Immanueldavidckp/schematics/docs/housing/internal/housing-closed.png

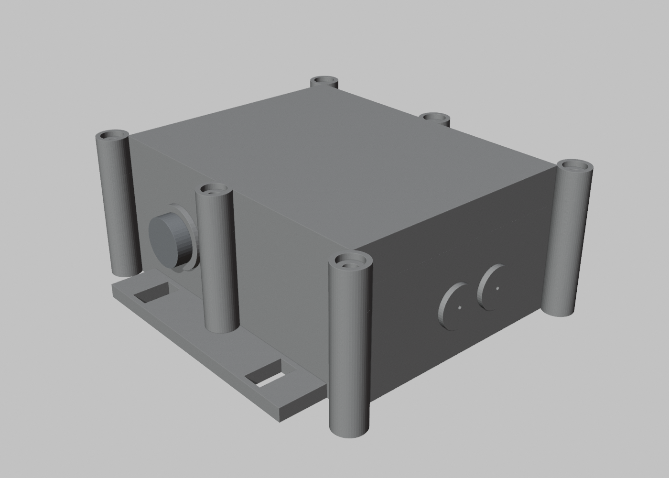
docs/housing/internal/housing-closed.png
