Immanueldavidckp/schematics/docs/housing/internal/housing-exploded.png

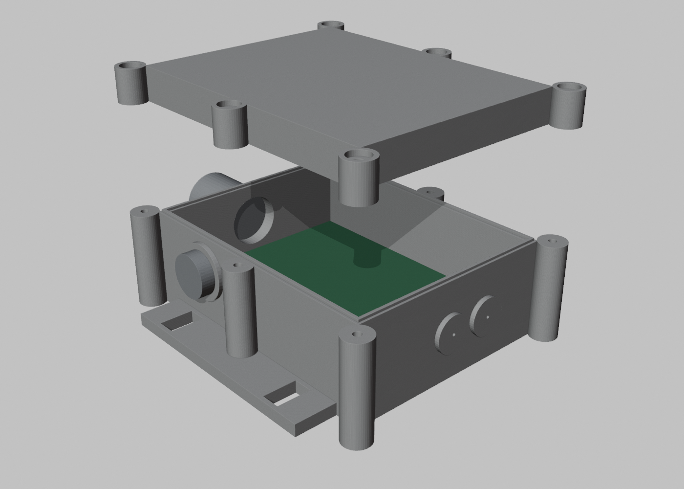
docs/housing/internal/housing-exploded.png
