Immanueldavidckp/schematics/docs/housing/internal/housing-sma-wall.png

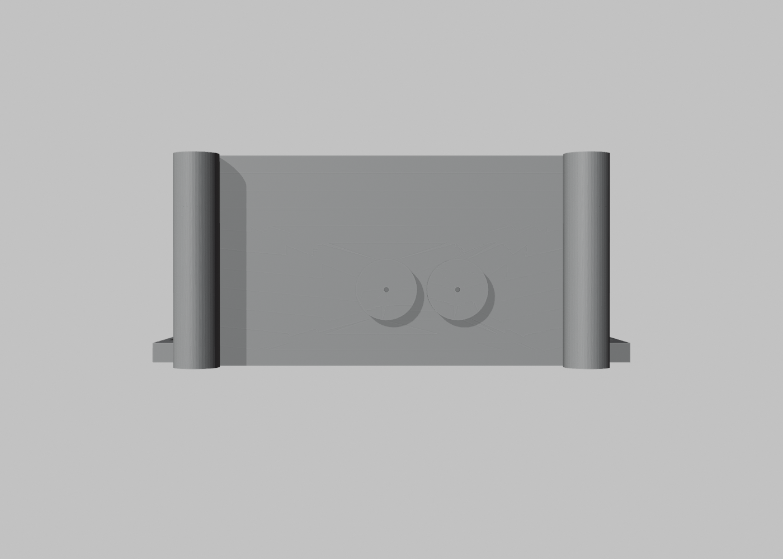
docs/housing/internal/housing-sma-wall.png
