Immanueldavidckp/schematics/tools/pcbroute_lv.py

#!/usr/bin/env python3
"""Route the remaining low-speed nets with the in-repo maze router (path b).

Approved after FreeRouting v2.4.1 was measured malfunctioning on this board
(design-log 2026-09-06). Quality gates, as instructed:

  1. Netclass rules enforced per net, DRC after each net, never loosened.
     A net whose routing raises the DRC error count is ROLLED BACK from the
     last good save and reported as failed - copper that cannot meet the
     rules does not stay on the board.
  2. Progress commit every 25 nets with completion %.
  3. Metrics: vias per net (flag > 4), total vias, routed length vs Manhattan
     distance per net (flag > 2.5x).
  4. No new copper on RF/HV/MV nets (those are locked and finished), none in
     the RF corridor, and none through the U1 lattice or U5 EP via fields.
  5. On plateau: stop with a per-net unrouted list and the blocking cause.

Architecture: pour-first. The board's power architecture IS the L2 GND plane
and the L3 islands (5V0 / SYS / 3V3 / VIN_B / VBAT_MODEM), so power-net pads
are connected by a stub + via into their plane wherever the pad sits over its
pour - one via, near-zero added length. Only what cannot reach a pour is
maze-routed on F/B.

Run:  PYTHONPATH=tools python3 tools/pcbroute_lv.py
"""
import ast
import heapq
import math
import os
import time
import re
import shutil
import subprocess
import sys
from collections import Counter, defaultdict

import pcbnew

sys.path.insert(0, os.path.dirname(os.path.abspath(__file__)))
from pcbgen import PROJ, PCB, mm, pt, canonicalise           # noqa: E402
from netclasses import HV, MV, RF, PWR, BULK                 # noqa: E402

to_mm = pcbnew.ToMM

RES = 0.10
CLR_EDGE = 0.50                 # copper-to-edge board rule for LV
LAST_GOOD = PCB + ".lastgood"
PROTECTED = set(HV) | set(MV) | set(RF)

# (track_width, clearance, via_dia, via_drill) per class
GEO = {
    # Default clearance is 0.20: that is what the board's stock Default
    # netclass carries, and the first run used 0.15 here - DRC (correctly)
    # rejected 12 nets against the class rule. Gate 1 works; the constant
    # was wrong.
    "Default":    (0.20, 0.20, 0.50, 0.30),
    "PWR":        (0.50, 0.20, 0.80, 0.40),
    "MODEM_BULK": (2.00, 0.20, 0.80, 0.40),
    "GND":        (0.50, 0.15, 0.50, 0.30),
}
CLS_CLR = {"HV": 0.60, "MV": 0.60, "RF": 0.30, "GND": 0.15,
           "PWR": 0.20, "MODEM_BULK": 0.20, "Default": 0.20}


def net_class(n):
    if n in HV:
        return "HV"
    if n in MV:
        return "MV"
    if n in RF:
        return "RF"
    if n in PWR:
        return "PWR"
    if n in BULK:
        return "MODEM_BULK"
    if n == "GND":
        return "GND"
    return "Default"


def drc_errors(path):
    """Non-ratsnest DRC error count (the per-net gate)."""
    rpt = path + ".drc"
    subprocess.run(["kicad-cli", "pcb", "drc", "--severity-error",
                    "-o", rpt, path], capture_output=True)
    text = open(rpt).read()
    kinds = re.findall(r"^\[([a-z_]+)\]", text, re.M)
    os.unlink(rpt)
    return sum(1 for k in kinds if k != "unconnected_items")


def git_progress(msg):
    subprocess.run(["git", "-C", PROJ, "add", os.path.basename(PCB)],
                   capture_output=True)
    subprocess.run(["git", "-C", PROJ, "commit", "-q", "-m",
                    msg + "\n\nCo-Authored-By: Claude Opus 5 (1M context) "
                    "<noreply@anthropic.com>"], capture_output=True)


def main(single_net=None, rip=None):
    # --rip: negotiation for the endgame. A net that fails with walled pad
    # entries lost its lanes to nets routed EARLIER (measured: C5.1/NRST had
    # 0/196 free start cells, sealed by VBAT_SENSE, CANH_T and GND vias that
    # are each individually legal). The named nets' UNLOCKED copper near the
    # starved net's pads is removed TEXTUALLY (board.Remove() poisons the
    # SWIG wrappers on Python 3.14 - measured core dumps; the adopt tool's
    # file-level rip is the proven pattern), the ripped copy is loaded, the
    # starved net routes FIRST, the ripped signal nets after. All-or-nothing:
    # any failure exits without saving, so the real board file never holds a
    # ripped-but-unrouted state. No rule changes - only the ORDER in which
    # the same rules are satisfied.
    if rip:
        from pcbgen import _split_forms
        rip = [n for n in rip if n not in PROTECTED]
        pre = pcbnew.LoadBoard(PCB)
        anchors_r = [(p.GetPosition().x / 1e6, p.GetPosition().y / 1e6)
                     for f in pre.GetFootprints()
                     for p in f.Pads() if p.GetNetname() == single_net]
        del pre
        RIP_R = float(os.environ.get("LV_RIP_R", "4"))
        txt = open(PCB, encoding="utf-8").read()
        body = txt[txt.index("\n") + 1: txt.rstrip().rfind(")")]
        kept, n_rip = [], 0
        for fo in _split_forms(body):
            tag = re.match(r"\(\s*([A-Za-z_0-9]+)", fo).group(1)
            drop = False
            if tag in ("segment", "via") and "(locked yes)" not in fo:
                mnet = re.search(r'\(net "([^"]*)"\)', fo)
                mxy = re.search(r"\((?:start|at) ([-\d.]+) ([-\d.]+)\)", fo)
                if mnet and mxy and mnet.group(1) in rip:
                    fx, fy = float(mxy.group(1)), float(mxy.group(2))
                    drop = any(abs(fx - ax) < RIP_R and abs(fy - ay) < RIP_R
                               for ax, ay in anchors_r)
            if drop:
                n_rip += 1
            else:
                kept.append(fo)
        head = txt[:txt.index("\n") + 1]
        tail = txt[txt.rstrip().rfind(")"):]
        # keep the .kicad_pcb extension: LoadBoard picks its format plugin
        # from the extension and returns None for anything else
        riptmp = PCB[:-len(".kicad_pcb")] + "-riptmp.kicad_pcb"
        open(riptmp, "w", encoding="utf-8").write(head + "".join(kept) + tail)
        print(f"ripped {n_rip} unlocked items of {sorted(rip)} "
              f"within {RIP_R:.0f} mm of {single_net}")
        board = pcbnew.LoadBoard(riptmp)
        os.unlink(riptmp)
    else:
        board = pcbnew.LoadBoard(PCB)
    LAYERS = [pcbnew.F_Cu, pcbnew.B_Cu]

    bb = board.GetBoardEdgesBoundingBox()
    x0, y0 = to_mm(bb.GetLeft()), to_mm(bb.GetTop())
    x1, y1 = to_mm(bb.GetRight()), to_mm(bb.GetBottom())
    NX, NY = int((x1 - x0) / RES) + 1, int((y1 - y0) / RES) + 1
    print(f"grid {NX} x {NY} at {RES} mm")

    def cell(x, y):
        return (int(round((x - x0) / RES)), int(round((y - y0) / RES)))

    def pos(ix, iy):
        return (x0 + ix * RES, y0 + iy * RES)

    # ---- no-go regions (both layers, for ALL new copper) -----------------
    nogo = []
    # RF corridor: everything outboard of x = 76.8 is CPWG + fence + U.FL
    nogo.append((76.8, y0, x1, y1, "RF corridor"))
    for ref, pads in (("U1", [str(i) for i in range(85, 113)]), ("U5", ["9"])):
        fp = next(f for f in board.GetFootprints() if f.GetReference() == ref)
        xs, ys, xe, ye = 1e9, 1e9, -1e9, -1e9
        for p in fp.Pads():
            if p.GetNumber() in pads:
                b2 = p.GetBoundingBox()
                xs = min(xs, to_mm(b2.GetLeft())); ys = min(ys, to_mm(b2.GetTop()))
                xe = max(xe, to_mm(b2.GetRight())); ye = max(ye, to_mm(b2.GetBottom()))
        nogo.append((xs - 0.3, ys - 0.3, xe + 0.3, ye + 0.3, ref + " via field"))
    for r in nogo:
        print(f"  no-go: {r[4]}  x {r[0]:.1f}..{r[2]:.1f} y {r[1]:.1f}..{r[3]:.1f}")

    # ---- obstacles --------------------------------------------------------
    # (net, layers, x, y, hw, hh)
    obst = []
    for f in board.GetFootprints():
        for p in f.Pads():
            b2 = p.GetBoundingBox()
            obst.append((p.GetNetname(), [l for l in p.GetLayerSet().CuStack()],
                         to_mm(b2.GetCenter().x), to_mm(b2.GetCenter().y),
                         to_mm(b2.GetWidth()) / 2, to_mm(b2.GetHeight()) / 2,
                         f.GetReference()))
    for t in board.GetTracks():
        if isinstance(t, pcbnew.PCB_VIA):
            obst.append((t.GetNetname(), LAYERS,
                         to_mm(t.GetPosition().x), to_mm(t.GetPosition().y),
                         to_mm(t.GetWidth()) / 2, to_mm(t.GetWidth()) / 2, ""))
        else:
            a, b2 = t.GetStart(), t.GetEnd()
            w = to_mm(t.GetWidth()) / 2
            ax, ay, bx, by = to_mm(a.x), to_mm(a.y), to_mm(b2.x), to_mm(b2.y)
            n = max(1, int(math.hypot(bx - ax, by - ay) / RES))
            for i in range(n + 1):
                tt = i / n
                # the true layer is kept even when it is an INNER one:
                # FreeRouting routes on GND_L2/PWR_L3, and a through-via
                # must clear that copper (measured: MODEM_BULK vias landed
                # 0.05..0.15 mm from SIM_RST on GND_L2 - invisible to a
                # 2-layer grid model)
                obst.append((t.GetNetname(), [t.GetLayer()],
                             ax + (bx - ax) * tt, ay + (by - ay) * tt, w, w, ""))
    print(f"obstacles: {len(obst)}")
    placed = []

    def build(netname, my_clr, half, via_mode=False):
        """via_mode: the grid gates VIA sites - a through via lands on every
        copper layer, so inner-layer obstacles block BOTH surface grids."""
        grids = [bytearray(NX * NY) for _ in LAYERS]
        trace = None
        if os.environ.get("LV_TRACE"):
            tx, ty = map(float, os.environ["LV_TRACE"].split(","))
            trace = cell(tx, ty)

        def block(g, ox, oy, rx, ry):
            # nogo/edge regions only: plain rectangles
            i0 = int(math.floor((ox - rx - x0) / RES))
            j0 = int(math.floor((oy - ry - y0) / RES))
            i1 = int(math.ceil((ox + rx - x0) / RES))
            j1 = int(math.ceil((oy + ry - y0) / RES))
            for j in range(max(0, j0), min(NY - 1, j1) + 1):
                row = j * NX
                for i in range(max(0, i0), min(NX - 1, i1) + 1):
                    g[row + i] = 1

        def block_pad(g, ox, oy, hw, hh, reach):
            # EXACT distance to the copper rectangle, like DRC measures it.
            # A box halo overestimates the corners by (sqrt(2)-1)*reach - up
            # to ~0.2 mm - and that inflation is precisely what erased the
            # legal diagonal passages around the U5/U6/U7 pin fields
            # (27/113 routed, everything else walled in).
            r2 = reach * reach
            i0 = int(math.floor((ox - hw - reach - x0) / RES))
            j0 = int(math.floor((oy - hh - reach - y0) / RES))
            i1 = int(math.ceil((ox + hw + reach - x0) / RES))
            j1 = int(math.ceil((oy + hh + reach - y0) / RES))
            for j in range(max(0, j0), min(NY - 1, j1) + 1):
                row = j * NX
                py = y0 + j * RES
                dy = abs(py - oy) - hh
                if dy < 0:
                    dy = 0.0
                dy2 = dy * dy
                for i in range(max(0, i0), min(NX - 1, i1) + 1):
                    px = x0 + i * RES
                    dx = abs(px - ox) - hw
                    if dx < 0:
                        dx = 0.0
                    if dx * dx + dy2 < r2 - 1e-12:
                        g[row + i] = 1

        for onet, lays, ox, oy, hw, hh, _oref in obst + placed:
            if onet == netname:
                continue
            oc = net_class(onet) if onet else "HV"
            clr = max(my_clr, CLS_CLR.get(oc, 0.15))
            # the 1.5 mm HV-to-LV rule: HV copper in the left strip of
            # HV_ZONE (x < 20; the buck arm is the BUCK_HV rescope at 0.60)
            if oc == "HV" and ox < 20.0:
                clr = 1.50
            inner = via_mode and any(l not in (pcbnew.F_Cu, pcbnew.B_Cu)
                                     for l in lays)
            for li, lay in enumerate(LAYERS):
                if not inner and lay not in lays:
                    continue
                if trace is not None and \
                        abs(ox - (x0 + trace[0] * RES)) <= hw + clr + half and \
                        abs(oy - (y0 + trace[1] * RES)) <= hh + clr + half:
                    print(f"      TRACE L{li} blocked by [{onet}] ref={_oref!r} "
                          f"at ({ox:.2f},{oy:.2f}) hw={hw:.2f} hh={hh:.2f} "
                          f"clr={clr:.2f}")
                block_pad(grids[li], ox, oy, hw, hh, clr + half)
        for gx0, gy0, gx1, gy1, _n in nogo:
            for g in grids:
                block(g, (gx0 + gx1) / 2, (gy0 + gy1) / 2,
                      (gx1 - gx0) / 2 + half, (gy1 - gy0) / 2 + half)
        e = int(math.ceil((CLR_EDGE + half) / RES - 1e-9)) + 1
        for g in grids:
            for j in range(NY):
                row = j * NX
                for i in range(NX):
                    if i < e or i >= NX - e or j < e or j >= NY - e:
                        g[row + i] = 1
        return grids

    def open_pad_entries(netname, tg, half):
        """Unblock the legal axial entry lane into each of this net's pads.

        A 0.5 mm-pitch LQFP pad has a legal entry: a track on the pad's long
        axis keeps 0.5 - 0.15 - half >= class clearance to the neighbouring
        pins. But that window is a +-0.05 mm line, and the box halos of the
        neighbours bury it - measured: U2.44 had 0/48 free goal cells while
        the flood reached 268k cells everywhere else. This opens the axis
        lane ON the pad plus up to 12 cells beyond each tip, re-verifying
        every lane cell against all obstacles EXCEPT sibling pads of the
        same footprint (the axial geometry to siblings is legal by
        construction; anything else - another part's pad, a via, a track -
        still blocks)."""
        mypads = [(o, r) for o in obst
                  for r in [o[6]] if o[0] == netname and o[6]]
        for (onet, lays, cx, cy, hw, hh, ref), _r in mypads:
            vert = hh >= hw
            both = abs(hh - hw) < 0.2      # round/square (THT) pads: 2 lanes
            # the ENTRY hop is emitted at w_hop = min(class w, pad_cap), so
            # cells near this pad are judged with the effective half-width,
            # not the class one - that mismatch is the whole reason lanes
            # near siblings are legal at all
            half_eff = min(half, max(0.20, min(2 * hw, 2 * hh)) / 2)
            # Sibling pads are excluded from lane blocking ONLY when they are
            # LATERAL neighbours - offset perpendicular to the lane axis, the
            # single-row case where the axial geometry is legal at class
            # clearance by construction. A sibling AHEAD along the lane must
            # still block: on U3's LGA grid the 3V3 lane extended straight
            # through the IMU's GND and NC pads (measured: shorting_items).
            # HV-in-strip siblings always block (1.5 mm rule, no exception).
            def sib_skip(o, axis):
                """True when sibling o may be ignored for THIS lane axis.

                Per-lane, and ARITHMETIC, not faith: a lateral sibling is
                skippable only when the lane's copper actually clears it -
                at U3's 0.5 mm LGA pitch a PWR-width entry has zero margin
                and 'legal by construction' measured 0.11 mm (regressions).
                0.055 covers the half-cell grid snap; the extra RES/(2*sqrt2)
                covers diagonal sag through force-opened lane cells, where
                the A* corner-cut test cannot see the wall (measured: a 3V3
                elbow at 0.190 mm from U2.23 against the 0.20 rule)."""
                if o[6] != ref:
                    return False
                if o[0] in HV and o[2] < 20.0:
                    return False          # HV-in-strip: 1.5 mm rule, no pass
                oc2 = net_class(o[0]) if o[0] else "HV"
                need = max(CLS_CLR.get(net_class(netname), 0.2),
                           CLS_CLR.get(oc2, 0.15)) + half + 0.055 + \
                    RES / (2.0 * math.sqrt(2.0))
                if axis == "v":
                    return abs(o[3] - cy) <= hh + 0.15 and \
                        (abs(o[2] - cx) - o[4]) >= need
                return abs(o[2] - cx) <= hw + 0.15 and \
                    (abs(o[3] - cy) - o[5]) >= need

            near = [o for o in obst + placed
                    if o[0] != netname
                    and abs(o[2] - cx) < 4.0 and abs(o[3] - cy) < 4.0]

            def lane_cell_ok(px, py, lay, axis):
                for o in near:
                    on2, l2, ox, oy, ohw, ohh, _r = o
                    if lay not in l2:
                        continue
                    oc = net_class(on2) if on2 else "HV"
                    clr = max(CLS_CLR.get(net_class(netname), 0.2),
                              CLS_CLR.get(oc, 0.15))
                    if on2 in HV and ox < 20.0:
                        clr = 1.50
                    ddx = max(abs(px - ox) - ohw, 0.0)
                    ddy = max(abs(py - oy) - ohh, 0.0)
                    d2 = ddx * ddx + ddy * ddy
                    if d2 >= (clr + half) ** 2 - 1e-12:
                        continue          # clear at class width
                    # sibling exemption, EXACT and per cell: the pad-level
                    # arithmetic approved lanes whose actual row sits off the
                    # pad axis (measured 0.190 mm to U2.23 vs the 0.20 rule,
                    # twice). An opened cell must clear the sibling FOR REAL
                    # at the emitted entry width (w_hop), plus diagonal sag -
                    # opened cells bypass the A* corner-cut wall test.
                    if sib_skip(o, axis) and \
                            d2 >= (clr + half_eff +
                                   RES / (2.0 * math.sqrt(2.0))) ** 2:
                        continue
                    return False
                for gx0, gy0, gx1, gy1, _n in nogo:
                    if gx0 - half <= px <= gx1 + half and \
                            gy0 - half <= py <= gy1 + half:
                        return False
                return True

            for li, lay in enumerate(LAYERS):
                if lay not in lays:
                    continue
                if vert or both:
                    ci = int(round((cx - x0) / RES))
                    j0 = int(round((cy - hh - y0) / RES)) - 25
                    j1 = int(round((cy + hh - y0) / RES)) + 25
                    for j in range(max(1, j0), min(NY - 2, j1) + 1):
                        px, py = pos(ci, j)
                        # every lane cell is verified - including on-pad
                        # cells, because a track on J1.4's own pad can still
                        # sit closer than 1.5 mm to the HV pin next to it
                        if lane_cell_ok(px, py, lay, "v"):
                            tg[li][j * NX + ci] = 0
                if (not vert) or both:
                    cj = int(round((cy - y0) / RES))
                    i0 = int(round((cx - hw - x0) / RES)) - 25
                    i1 = int(round((cx + hw - x0) / RES)) + 25
                    for i in range(max(1, i0), min(NX - 2, i1) + 1):
                        px, py = pos(i, cj)
                        if lane_cell_ok(px, py, lay, "h"):
                            tg[li][cj * NX + i] = 0

    def astar(tg, vg, starts, goals):
        goalset = set(goals)
        if not goalset:
            return None
        gx = sum(g[1] for g in goals) / len(goals)
        gy = sum(g[2] for g in goals) / len(goals)
        openh, best, came = [], {}, {}
        for s in starts:
            best[s] = 0.0
            heapq.heappush(openh, (math.hypot(s[1] - gx, s[2] - gy), 0.0, s, None))
        NB = [(1, 0, 1.0), (-1, 0, 1.0), (0, 1, 1.0), (0, -1, 1.0),
              (1, 1, 1.4142), (1, -1, 1.4142), (-1, 1, 1.4142), (-1, -1, 1.4142)]
        while openh:
            _, g, cur, parent = heapq.heappop(openh)
            if cur in came:
                continue
            came[cur] = parent
            if cur in goalset:
                path = [cur]
                while came[path[-1]] is not None:
                    path.append(came[path[-1]])
                return path[::-1]
            li, ix, iy = cur
            for dx, dy, w in NB:
                nx_, ny_ = ix + dx, iy + dy
                if not (0 <= nx_ < NX and 0 <= ny_ < NY) or tg[li][ny_ * NX + nx_]:
                    continue
                # no corner-cutting: a diagonal between two halo-legal cells
                # can pass RES/(2*sqrt(2)) closer to a pad corner than either
                # endpoint (measured: SYS at 0.1963 vs the 0.20 rule against
                # U9.2 - the +1 that killed every pour batch). Requiring both
                # orthogonal neighbours free keeps the swept segment inside
                # tested cells without shrinking any engineered lane.
                if dx and dy and (tg[li][iy * NX + nx_] or
                                  tg[li][ny_ * NX + ix]):
                    continue
                nxt, ng = (li, nx_, ny_), g + w
                if ng < best.get(nxt, 1e18):
                    best[nxt] = ng
                    heapq.heappush(openh, (ng + math.hypot(nx_ - gx, ny_ - gy),
                                           ng, nxt, cur))
            for lj in range(2):
                if lj == li or vg[lj][iy * NX + ix] or vg[li][iy * NX + ix]:
                    continue
                nxt, ng = (lj, ix, iy), g + 14
                if ng < best.get(nxt, 1e18):
                    best[nxt] = ng
                    heapq.heappush(openh, (ng + math.hypot(ix - gx, iy - gy),
                                           ng, nxt, cur))
        return None

    def pad_cells(p):
        b2 = p.GetBoundingBox()
        cx, cy = to_mm(b2.GetCenter().x), to_mm(b2.GetCenter().y)
        hw, hh = to_mm(b2.GetWidth()) / 2, to_mm(b2.GetHeight()) / 2
        lays = [l for l in p.GetLayerSet().CuStack()]
        out = []
        for li, lay in enumerate(LAYERS):
            if lay not in lays:
                continue
            i0, j0 = cell(cx - hw * 0.9, cy - hh * 0.9)
            i1, j1 = cell(cx + hw * 0.9, cy + hh * 0.9)
            for j in range(max(0, j0), min(NY - 1, j1) + 1):
                for i in range(max(0, i0), min(NX - 1, i1) + 1):
                    out.append((li, i, j))
        return out

    # ---- clusters: BFS over the connectivity graph's DIRECT edges --------
    # GetConnectedItems(item) with no type filter returns just the item, and
    # even typed queries return only DIRECTLY touching items (measured:
    # C81.1 -> 1 via, not the cluster). So the cluster is computed here: BFS
    # over per-type direct-edge queries, zone fills included.
    CONN_TYPES = (pcbnew.PCB_PAD_T, pcbnew.PCB_TRACE_T,
                  pcbnew.PCB_VIA_T, pcbnew.PCB_ZONE_T)

    def clusters(netname):
        conn = board.GetConnectivity()
        items = []
        for f in board.GetFootprints():
            for p in f.Pads():
                if p.GetNetname() == netname:
                    items.append(p)
        for t in board.GetTracks():
            if t.GetNetname() == netname:
                items.append(t)
        for z in board.Zones():
            if not z.GetIsRuleArea() and z.GetNetname() == netname:
                items.append(z)
        byid = {i.m_Uuid.AsString(): i for i in items}
        seen, out = set(), []
        for k in byid:
            if k in seen:
                continue
            stack, comp = [k], []
            while stack:
                c = stack.pop()
                if c in seen:
                    continue
                seen.add(c)
                comp.append(c)
                it = byid[c]
                for T in CONN_TYPES:
                    for j in conn.GetConnectedItems(it, T):
                        jk = j.m_Uuid.AsString()
                        if jk in byid and jk not in seen:
                            stack.append(jk)
            group = [byid[c] for c in comp
                     if byid[c].Type() == pcbnew.PCB_PAD_T]
            extra = [byid[c] for c in comp
                     if byid[c].Type() in (pcbnew.PCB_TRACE_T,
                                           pcbnew.PCB_VIA_T)]
            has_zone = any(byid[c].Type() == pcbnew.PCB_ZONE_T for c in comp)
            out.append((group or [byid[comp[0]]], extra, has_zone))
        # the pour-connected cluster first, then by pad count. The tap loop
        # must SKIP zone-connected clusters: without the flag it re-tapped
        # the already-merged cluster every round (all size-1 clusters sort
        # arbitrarily) and the count never dropped.
        out.sort(key=lambda ge: (not ge[2], -len(ge[0])))
        return out

    # ---- emit helpers -----------------------------------------------------
    stats = {"vias": 0}

    def emit_path(path, net, w, vd, vdr):
        nv, tl = 0, 0.0
        runs, prev = [], None
        for cur in path:
            if prev is not None:
                if prev[0] != cur[0]:
                    runs.append(["via", cur, None, None])
                else:
                    d = (cur[1] - prev[1], cur[2] - prev[2])
                    if runs and runs[-1][0] == "seg" and \
                            runs[-1][3] == (prev[0], d) and runs[-1][2] == prev:
                        runs[-1][2] = cur
                    else:
                        runs.append(["seg", prev, cur, (prev[0], d)])
            prev = cur
        for kind, a, b2, meta in runs:
            if kind == "via":
                li, ix, iy = a
                v = pcbnew.PCB_VIA(board)
                v.SetPosition(pt(*pos(ix, iy)))
                v.SetWidth(mm(vd)); v.SetDrill(mm(vdr))
                v.SetNet(net); v.SetLayerPair(pcbnew.F_Cu, pcbnew.B_Cu)
                board.Add(v)
                nv += 1
                placed.append((net.GetNetname(), LAYERS, *pos(ix, iy),
                               vd / 2, vd / 2, ""))
            else:
                li = meta[0]
                t = pcbnew.PCB_TRACK(board)
                t.SetStart(pt(*pos(*a[1:]))); t.SetEnd(pt(*pos(*b2[1:])))
                t.SetWidth(mm(w)); t.SetLayer(LAYERS[li]); t.SetNet(net)
                board.Add(t)
                seg = math.hypot(b2[1] - a[1], b2[2] - a[2]) * RES
                tl += seg
                n_ = max(abs(b2[1] - a[1]), abs(b2[2] - a[2]), 1)
                for k in range(n_ + 1):
                    fx = a[1] + (b2[1] - a[1]) * k / n_
                    fy = a[2] + (b2[2] - a[2]) * k / n_
                    placed.append((net.GetNetname(), [LAYERS[li]],
                                   x0 + fx * RES, y0 + fy * RES, w / 2, w / 2, ""))
        stats["vias"] += nv
        return nv, tl

    # ---- pour taps ---------------------------------------------------------
    # net -> [(zone, inner_layer, window)] - the FILLED polygon is what a tap
    # via must hit. The first run tested the bounding box only: vias landed in
    # fill voids (clearance holes around other copper), never connected, the
    # cluster count never dropped, and each power net sprayed up to 12 dead
    # vias that then walled off every later net.
    pours = defaultdict(list)
    for z in board.Zones():
        if z.GetIsRuleArea():
            continue
        for l in z.GetLayerSet().CuStack():
            if l in (pcbnew.F_Cu, pcbnew.B_Cu):
                continue
            zb = z.GetBoundingBox()
            pours[z.GetNetname()].append(
                (z, l, (to_mm(zb.GetLeft()) + 0.6, to_mm(zb.GetTop()) + 0.6,
                        to_mm(zb.GetRight()) - 0.6, to_mm(zb.GetBottom()) - 0.6)))

    def tap_pour(netname, group, tg, vg, vd, vdr, w, net):
        """Maze a stub from the cluster to a via site that HITS the net's
        filled inner-layer pour. Returns the emitted items (for rollback) or
        None. The via site is verified against the FILLED polygon and the
        stub is a routed path, not a blind line."""
        zl = pours.get(netname)
        if not zl:
            return None
        goals = []
        for z, lay, (wx0, wy0, wx1, wy1) in zl:
            i0, j0 = cell(wx0, wy0)
            i1, j1 = cell(wx1, wy1)
            for j in range(max(0, j0), min(NY - 1, j1) + 1):
                for i in range(max(0, i0), min(NX - 1, i1) + 1):
                    if vg[0][j * NX + i] or vg[1][j * NX + i]:
                        continue
                    x, y = pos(i, j)
                    if z.HitTestFilledArea(lay, pt(x, y), 0):
                        goals.append((0, i, j))
                        goals.append((1, i, j))
        if not goals:
            return None
        starts = []
        for p in group:
            starts += pad_cells(p)
        path = astar(tg, vg, starts, set(goals))
        if path is None:
            return None
        mark = len(placed)
        items_before = set(id(t) for t in board.GetTracks())
        emit_path(path, net, w, vd, vdr)
        # a through via at the endpoint reaches the inner pour; if the path
        # already ended with a layer change, that via is the tap
        li, ix, iy = path[-1]
        need_via = len(path) < 2 or path[-2][0] == path[-1][0]
        if need_via:
            v = pcbnew.PCB_VIA(board)
            v.SetPosition(pt(*pos(ix, iy)))
            v.SetWidth(mm(vd)); v.SetDrill(mm(vdr))
            v.SetNet(net); v.SetLayerPair(pcbnew.F_Cu, pcbnew.B_Cu)
            board.Add(v)
            stats["vias"] += 1
            placed.append((netname, LAYERS, *pos(ix, iy), vd / 2, vd / 2, ""))
        new_items = [t for t in board.GetTracks() if id(t) not in items_before]
        return new_items, mark

    # GND: the L2 solid plane
    for z in board.Zones():
        if z.GetZoneName() == "L2_GND_solid":
            pours["GND"] = [(z, board.GetLayerID("In1.Cu"),
                             (x0 + 2.0, y0 + 2.0, x1 - 2.0, y1 - 2.0))]

    # ---- the work list -----------------------------------------------------
    def refill():
        board.BuildListOfNets()
        pcbnew.ZONE_FILLER(board).Fill(board.Zones())

    def refresh_connectivity():
        board.BuildConnectivity()

    # ---- island taps -------------------------------------------------------
    # KiCad's connectivity treats a ZONE as ONE item, so a pour that fills as
    # several disconnected islands still merges its clusters()' BFS into one
    # cluster - route_net() then reports the net complete while DRC counts an
    # unconnected edge per island split (measured: 104 of the 150-edge v11
    # plateau were exactly these, on GND/3V3/5V0/SYS). A filled island with no
    # net via / PTH pad inside it can only be reached through its own copper:
    # bond it with one via at a spot where another fill of the same net (the
    # L2 plane, an L3 island, or the opposite surface pour) lies underneath.

    def net_anchors(netname):
        anchors = [t.GetPosition() for t in board.GetTracks()
                   if t.GetNetname() == netname
                   and t.GetClass() == "PCB_VIA"]
        for f in board.GetFootprints():
            for p in f.Pads():
                if p.GetNetname() == netname and \
                        p.GetAttribute() == pcbnew.PAD_ATTRIB_PTH:
                    anchors.append(p.GetPosition())
        return anchors

    def net_fills(netname):
        out = []
        for z in board.Zones():
            if z.GetIsRuleArea() or z.GetNetname() != netname:
                continue
            for lay in z.GetLayerSet().CuStack():
                out.append((z, lay))
        return out

    def orphan_islands(netname):
        """(zone, layer, outline-index, bbox) of every fill island holding no
        via / through pad of the net."""
        anchors = net_anchors(netname)
        out = []
        for z, lay in net_fills(netname):
            polys = z.GetFilledPolysList(lay)
            for oi in range(polys.OutlineCount()):
                bb = polys.Outline(oi).BBox()
                if any(bb.Contains(a) and polys.Contains(a, oi)
                       for a in anchors):
                    continue
                out.append((z, lay, oi, bb))
        return out

    def island_taps(netname, net, vd, vdr, my_clr):
        """Place the bonding vias. Returns how many were added; refills and
        rebuilds connectivity when any were."""
        orphans = orphan_islands(netname)
        if not orphans:
            return 0
        vg = build(netname, my_clr, vd / 2, via_mode=True)
        fills = net_fills(netname)
        added = []
        for z, lay, oi, bb in orphans:
            polys = z.GetFilledPolysList(lay)
            i0, j0 = cell(to_mm(bb.GetLeft()), to_mm(bb.GetTop()))
            i1, j1 = cell(to_mm(bb.GetRight()), to_mm(bb.GetBottom()))
            spot = None
            for j in range(max(0, j0), min(NY - 1, j1) + 1):
                for i in range(max(0, i0), min(NX - 1, i1) + 1):
                    if vg[0][j * NX + i] or vg[1][j * NX + i]:
                        continue
                    x, y = pos(i, j)
                    # a fresh via is not in vg: keep new ones apart
                    if any((x - ax) ** 2 + (y - ay) ** 2 < 0.9 ** 2
                           for ax, ay in added):
                        continue
                    p_ = pt(x, y)
                    if not polys.Contains(p_, oi):
                        continue
                    if any(z2.HitTestFilledArea(l2, p_, 0)
                           for z2, l2 in fills
                           if not (z2 is z and l2 == lay)):
                        spot = (x, y)
                        break
                if spot:
                    break
            if spot is None:
                if os.environ.get("LV_DEBUG"):
                    print(f"    DEBUG island (layer {lay}) at "
                          f"({to_mm(bb.GetLeft()):.1f},{to_mm(bb.GetTop()):.1f})"
                          f" has no legal tap spot")
                continue
            v = pcbnew.PCB_VIA(board)
            v.SetPosition(pt(*spot))
            v.SetWidth(mm(vd)); v.SetDrill(mm(vdr))
            v.SetNet(net); v.SetLayerPair(pcbnew.F_Cu, pcbnew.B_Cu)
            board.Add(v)
            stats["vias"] += 1
            placed.append((netname, LAYERS, *spot, vd / 2, vd / 2, ""))
            added.append(spot)
        if added:
            if os.environ.get("LV_DEBUG"):
                print(f"    DEBUG island taps: {len(added)} vias "
                      f"({len(orphans)} orphan islands)")
            refill()
            refresh_connectivity()
        return len(added)

    if single_net == "--finish--":
        refill()
        pcbnew.SaveBoard(PCB, board)
        canonicalise(PCB)
        print("CHILD_FINISHED")
        return

    refill()
    refresh_connectivity()

    if single_net == "--list--":
        all_nets = sorted({p.GetNetname() for f in board.GetFootprints()
                           for p in f.Pads()
                           if p.GetNetname() and p.GetNetname() not in PROTECTED})
        for n in all_nets:
            if len(clusters(n)) > 1 or orphan_islands(n):
                print(f"TODO {n}")
        return

    if single_net == "--spans--":
        all_nets = {p.GetNetname() for f in board.GetFootprints()
                    for p in f.Pads()
                    if p.GetNetname() and p.GetNetname() not in PROTECTED}
        for n in sorted(all_nets):
            xs, ys = [], []
            for f in board.GetFootprints():
                for p in f.Pads():
                    if p.GetNetname() == n:
                        xs.append(to_mm(p.GetPosition().x))
                        ys.append(to_mm(p.GetPosition().y))
            if len(xs) > 1:
                print(f"SPAN {max(xs)-min(xs)+max(ys)-min(ys):.1f} {n}")
        return

    def route_net(netname):
        """Route one net to a single cluster. On failure ALL of this net's
        partial copper is REMOVED (board.Remove on tracks/vias is safe -
        verified; the footprint segfault in SKILL.md does not apply) so a
        failed net cannot wall off the nets after it. Returns
        (ok, cause, vias, length, manhattan)."""
        cls = net_class(netname)
        w, my_clr, vd, vdr = GEO[cls]
        net = board.FindNet(netname)
        nv_net, tl_net, man_net = 0, 0.0, 0.0

        def pad_cap(p):
            b2 = p.GetBoundingBox()
            return max(0.20, min(to_mm(b2.GetWidth()), to_mm(b2.GetHeight())))

        def fail(cause):
            # No in-memory rollback (board.Remove crashes at scale). The
            # child decides: with zero progress it exits unsaved; with
            # partial progress it SAVES and reports CHILD_PARTIAL - the
            # copper is legal, only the remaining edges requeue.
            return False, cause, nv_net, tl_net, man_net

        # The FIRST tap into a virgin pour does not reduce the pad-cluster
        # count (it merges a cluster with the pour, not with another pad
        # cluster) - the drop comes when the second cluster taps in. So the
        # stagnation window is 3 rounds, not 1.
        nv_net += island_taps(netname, net, vd, vdr, my_clr)

        best_cl, stagnant = None, 0
        for _round in range(40):
            refresh_connectivity()
            cl = clusters(netname)
            if len(cl) <= 1:
                if orphan_islands(netname):
                    return fail("orphan pour islands with no legal tap spot")
                return True, "", nv_net, tl_net, man_net
            if os.environ.get("LV_DEBUG"):
                sizes = [len(g) for g, _e, _z in cl][:8]
                print(f"    DEBUG round {_round}: {len(cl)} clusters "
                      f"(pad counts {sizes})")
            if best_cl is None or len(cl) < best_cl:
                best_cl, stagnant = len(cl), 0
            else:
                stagnant += 1
                if stagnant >= 3:
                    return fail(f"cluster count stuck at {len(cl)}")
            tg = build(netname, my_clr, w / 2)
            vg = build(netname, my_clr, vd / 2, via_mode=True)
            open_pad_entries(netname, tg, w / 2)
            tapped = False
            for group, _extra, hz in cl[1:]:
                if hz:
                    continue          # already reaches the pour
                r = tap_pour(netname, group, tg, vg, vd, vdr, w, net)
                if r is not None:
                    if os.environ.get("LV_DEBUG"):
                        gp = group[0]
                        nm = "?"
                        try:
                            nm = (gp.GetParentFootprint().GetReference()
                                  + "." + gp.GetPadNumber())
                        except Exception:
                            nm = gp.GetClass()
                        items2, _mk = r
                        vpos = [f"({to_mm(t.GetPosition().x):.1f},"
                                f"{to_mm(t.GetPosition().y):.1f})"
                                for t in items2
                                if isinstance(t, pcbnew.PCB_VIA)]
                        print(f"    DEBUG tapped {nm} vias at "
                              f"{vpos}")
                    nv_net += 1
                    tapped = True
                    break
            if tapped:
                last_cl = len(cl)
                continue
            pairs = []
            for i in range(len(cl)):
                for j in range(i + 1, len(cl)):
                    for pa in cl[i][0]:
                        for pb in cl[j][0]:
                            d = (pa.GetPosition() - pb.GetPosition()).EuclideanNorm()
                            pairs.append((d, i, j, pa, pb))
            if not pairs:
                return fail("no pad pair")
            pairs.sort(key=lambda t: t[0])
            # try up to 12 candidate pairs: the closest pair's endpoint can
            # be pocketed while another cluster pair routes fine - and on the
            # multi-cluster pour nets, quitting at the 4th candidate left
            # every easy pair BEHIND the first hard one unrouted (measured:
            # 3V3 stalled whole at U3.5->U3.10 with 24 other edges pending)
            path = None
            for _d, i, j, pa, pb in pairs[:12]:
            # A 2.0 mm MODEM_BULK track cannot ENTER a 1210 pad cluster at
            # 0.2 clearance (measured: C81.1 goals 0/286 free). The last
            # approach is physically capped by the endpoint pad's own width -
            # the pad is the cross-section limit; the RAIL requirement is
            # carried by the pour and the wide mid-run.
            # min() of the endpoint caps: the hop must ENTER BOTH pads, and
            # a 1.5 mm track cannot enter an 0603 (measured on C43.1). The
            # rail current rides the pour; the last approach is pad-limited.
                w_hop = min(w, pad_cap(pa), pad_cap(pb))
                if w_hop < w:
                    tg = build(netname, my_clr, w_hop / 2)
                    open_pad_entries(netname, tg, w_hop / 2)
                starts = []
                for p in cl[i][0]:
                    starts += pad_cells(p)
                for it in cl[i][1]:
                    if isinstance(it, pcbnew.PCB_VIA):
                        c = cell(to_mm(it.GetPosition().x),
                                 to_mm(it.GetPosition().y))
                        starts += [(0, *c), (1, *c)]
                goals = []
                for p in cl[j][0]:
                    goals += pad_cells(p)
                path = astar(tg, vg, starts, goals)
                if path is not None:
                    break
                if w_hop < w:
                    # restore the class-width grid for the next candidate
                    tg = build(netname, my_clr, w / 2)
                    open_pad_entries(netname, tg, w / 2)
            if path is None and os.environ.get("LV_DEBUG"):
                free_s = sum(1 for li, i, j in starts if not tg[li][j * NX + i])
                free_g = sum(1 for li, i, j in goals if not tg[li][j * NX + i])
                print(f"    DEBUG starts {free_s}/{len(starts)} free, "
                      f"goals {free_g}/{len(goals)} free")
                # a SEALED terminal (0 free cells) is starved by the few nets
                # whose copper covers its own cells - name THOSE, not the
                # whole flood boundary: the global wall histogram dilutes the
                # actual sealers into noise (measured: U2.8 sealed by nets
                # that never reached the top-3 rip candidates)
                cls2 = net_class(netname)
                clr_half = GEO[cls2][0] / 2
                for label, cells, nfree in (("start", starts, free_s),
                                            ("goal", goals, free_g)):
                    if nfree > 0:
                        continue
                    seal = Counter()
                    for li, i, j in cells:
                        px, py = pos(i, j)
                        for on2, l2, ox, oy, ohw, ohh, _r in obst + placed:
                            if on2 == netname or LAYERS[li] not in l2:
                                continue
                            oc2 = net_class(on2) if on2 else "HV"
                            c2 = max(GEO[cls2][1], CLS_CLR.get(oc2, 0.15))
                            if on2 in HV and ox < 20.0:
                                c2 = 1.50
                            if abs(px - ox) <= ohw + c2 + clr_half and \
                                    abs(py - oy) <= ohh + c2 + clr_half:
                                seal[on2 or "netless"] += 1
                                break
                    print(f"    DEBUG pad seal ({label}): "
                          f"{dict(seal.most_common(5))}")
                from collections import deque
                seen, dq = set(), deque()
                for c in starts:
                    li, i, j = c
                    if not tg[li][j * NX + i]:
                        seen.add(c); dq.append(c)
                while dq:
                    li, i, j = dq.popleft()
                    for dx, dy in ((1,0),(-1,0),(0,1),(0,-1),
                                   (1,1),(1,-1),(-1,1),(-1,-1)):
                        ni, nj = i + dx, j + dy
                        if 0 <= ni < NX and 0 <= nj < NY and \
                                not tg[li][nj * NX + ni] and \
                                (li, ni, nj) not in seen:
                            seen.add((li, ni, nj)); dq.append((li, ni, nj))
                    lj = 1 - li
                    if not vg[lj][j * NX + i] and not vg[li][j * NX + i] \
                            and (lj, i, j) not in seen:
                        seen.add((lj, i, j)); dq.append((lj, i, j))
                xs = [pos(i, j) for li, i, j in list(seen)[:100000]]
                if xs:
                    print(f"    DEBUG flood {len(seen)} cells, x range "
                          f"{min(x for x,_ in xs):.1f}..{max(x for x,_ in xs):.1f}, "
                          f"y {min(y for _,y in xs):.1f}..{max(y for _,y in xs):.1f}")
                else:
                    print(f"    DEBUG flood 0 cells - ALL start cells blocked")
                # name the walls: which nets' halos form the pocket boundary
                cls = net_class(netname)
                my_clr = GEO[cls][1]
                half = GEO[cls][0] / 2
                wall = Counter()
                frontier = 0
                for (li, i, j) in list(seen)[:60000]:
                    for dx, dy in ((1,0),(-1,0),(0,1),(0,-1)):
                        ni, nj = i + dx, j + dy
                        if not (0 <= ni < NX and 0 <= nj < NY) or \
                                not tg[li][nj * NX + ni]:
                            continue
                        frontier += 1
                        if frontier > 4000:
                            break
                        px, py = pos(ni, nj)
                        hit = None
                        for on2, l2, ox, oy, ohw, ohh, oref in obst + placed:
                            if on2 == netname or LAYERS[li] not in l2:
                                continue
                            oc = net_class(on2) if on2 else "HV"
                            clr = max(my_clr, CLS_CLR.get(oc, 0.15))
                            if on2 in HV and ox < 20.0:
                                clr = 1.50
                            if abs(px - ox) <= ohw + clr + half and \
                                    abs(py - oy) <= ohh + clr + half:
                                hit = f"{on2 or 'netless'}"
                                break
                        wall[hit or "edge/nogo"] += 1
                    if frontier > 4000:
                        break
                print(f"    DEBUG pocket walls: "
                      f"{dict(wall.most_common(8))}")
                shown = 0
                for (li, i, j) in list(seen)[:60000]:
                    if shown >= 6:
                        break
                    for dx, dy in ((1,0),(-1,0),(0,1),(0,-1)):
                        ni, nj = i + dx, j + dy
                        if not (0 <= ni < NX and 0 <= nj < NY) or \
                                not tg[li][nj * NX + ni]:
                            continue
                        px, py = pos(ni, nj)
                        hit = None
                        for on2, l2, ox, oy, ohw, ohh, oref in obst + placed:
                            if on2 == netname or LAYERS[li] not in l2:
                                continue
                            oc = net_class(on2) if on2 else "HV"
                            clr = max(my_clr, CLS_CLR.get(oc, 0.15))
                            if on2 in HV and ox < 20.0:
                                clr = 1.50
                            if abs(px - ox) <= ohw + clr + half and \
                                    abs(py - oy) <= ohh + clr + half:
                                hit = on2
                                break
                        if hit is None:
                            print(f"    DEBUG unknown wall cell L{li} "
                                  f"({px:.2f},{py:.2f})")
                            shown += 1
                            break
            if path is None:
                cause = (f"no path "
                         f"{pa.GetParentFootprint().GetReference()}.{pa.GetNumber()}"
                         f" -> "
                         f"{pb.GetParentFootprint().GetReference()}.{pb.GetNumber()}")
                return fail(cause)
            nv, tl = emit_path(path, net, w_hop, vd, vdr)
            nv_net += nv
            tl_net += tl
            man_net += (abs(to_mm(pa.GetPosition().x - pb.GetPosition().x))
                        + abs(to_mm(pa.GetPosition().y - pb.GetPosition().y)))
            last_cl = len(cl)
        return fail("cluster count did not converge in 40 rounds")

    # child mode: route exactly one net. Full success saves and reports OK.
    # PARTIAL success also saves: a 42-pad net that closes 35 taps and then
    # hits one stubborn hop was previously discarded whole - 3V3 re-made and
    # re-lost ~35 connections every cycle. Partial copper is legal (the same
    # grids produced it); the remaining edges requeue and resume from the
    # saved state next pass.
    if rip:
        # starved net first, then the ripped SIGNAL nets. Ripped POUR nets
        # are NOT re-routed here (route_net on GND rebuilds grids for ~40
        # rounds and blows the retry budget) - they are reported for the
        # parent to requeue; their taps are cheap in their own child.
        seq = [single_net] + [n for n in rip if n not in pours]
        tot = [0, 0.0, 0.0]
        for nn in seq:
            refill()
            refresh_connectivity()
            ok, cause, nv, tl, man = route_net(nn)
            tot[0] += nv; tot[1] += tl; tot[2] += man
            if not ok:
                print(f"CHILD_FAIL rip-retry stalled on {nn}: {cause}")
                sys.exit(3)          # unsaved: the rip never reaches disk
        refill()
        pcbnew.SaveBoard(PCB, board)
        for nn in rip:
            if nn in pours:
                print(f"REQUEUE {nn}")
        print(f"CHILD_OK vias={tot[0]} len={tot[1]:.2f} man={tot[2]:.2f}")
        return

    ok, cause, nv, tl, man = route_net(single_net)
    if ok:
        refill()
        pcbnew.SaveBoard(PCB, board)
        print(f"CHILD_OK vias={nv} len={tl:.2f} man={man:.2f}")
        return
    if nv > 0 or tl > 0:
        refill()
        pcbnew.SaveBoard(PCB, board)
        print(f"CHILD_PARTIAL vias={nv} len={tl:.2f} man={man:.2f} cause={cause}")
        sys.exit(4)
    print(f"CHILD_FAIL {cause}")
    sys.exit(3)


def orchestrate():
    """Parent: per-net child processes. A child that fails (or crashes -
    pcbnew has done that) exits without saving, so the board file only ever
    contains fully-routed, gate-checked nets. No in-memory rollback exists
    because none is needed."""
    me = os.path.abspath(__file__)

    def child(args, timeout=900):
        return subprocess.run([sys.executable, "-u", me] + args,
                              capture_output=True, text=True, timeout=timeout)

    # LV_RIP_WINDOW="x0,y0,x1,y1": pocket restart. Rip ALL unlocked,
    # unprotected copper inside the window before routing, then route the
    # whole pocket from a clean slate with the starved nets FIRST (LV_FIRST).
    # Sequential routing starved them precisely because the flexible nets
    # went first and took the last lanes; hard-first inverts that. Textual
    # rip - same proven pattern as pcbroute_adopt.
    win = os.environ.get("LV_RIP_WINDOW")
    if win:
        from pcbgen import _split_forms
        wx0, wy0, wx1, wy1 = (float(v) for v in win.split(","))
        txt = open(PCB, encoding="utf-8").read()
        body = txt[txt.index("\n") + 1: txt.rstrip().rfind(")")]
        kept, n_rip = [], 0
        for fo in _split_forms(body):
            tag = re.match(r"\(\s*([A-Za-z_0-9]+)", fo).group(1)
            drop = False
            if tag in ("segment", "via") and "(locked yes)" not in fo:
                mnet = re.search(r'\(net "([^"]*)"\)', fo)
                mxy = re.search(r"\((?:start|at) ([-\d.]+) ([-\d.]+)\)", fo)
                if mnet and mxy and mnet.group(1) not in PROTECTED:
                    fx, fy = float(mxy.group(1)), float(mxy.group(2))
                    drop = wx0 < fx < wx1 and wy0 < fy < wy1
            if drop:
                n_rip += 1
            else:
                kept.append(fo)
        head = txt[:txt.index("\n") + 1]
        tail = txt[txt.rstrip().rfind(")"):]
        open(PCB, "w", encoding="utf-8").write(head + "".join(kept) + tail)
        print(f"POCKET RESTART: ripped {n_rip} unlocked items in "
              f"window {win}")
        child(["--finish"], timeout=600)     # refill + canonicalise

    r = child(["--list"])
    todo = [l.split(None, 1)[1] for l in r.stdout.splitlines()
            if l.startswith("TODO ")]
    total_ct = len(todo)
    print(f"nets needing work: {total_ct}")

    shutil.copyfile(PCB, LAST_GOOD)
    baseline = drc_errors(PCB)
    print(f"baseline DRC errors (non-ratsnest): {baseline}")

    # span per net, from a --spans child (longest first: the cross-board
    # corridors are the scarce resource - CANH from J1 to the transceiver
    # was walled in by its OWN termination nets routed before it)
    r = child(["--spans"])
    spans = {}
    for l in r.stdout.splitlines():
        if l.startswith("SPAN "):
            _, v, n = l.split(None, 2)
            spans[n] = float(v)
    metrics, failed = {}, {}
    done_ct = 0
    order = sorted(todo, key=lambda n: (net_class(n) != "MODEM_BULK",
                                        net_class(n) != "PWR",
                                        -spans.get(n, 0.0), n))
    first = [n for n in os.environ.get("LV_FIRST", "").split(";")
             if n and n in todo]
    if first:
        order = first + [n for n in order if n not in set(first)]
        print(f"hard-first override: {len(first)} net(s) lead the queue")
    queue = list(order)
    rip_plan = {}       # net -> wall nets to rip on its next attempt
    # Wall-clock cap: the chain's outer `timeout` was observed not to fire
    # (cycle 2 ran 15 h against a 25000 s cap), so the orchestrator enforces
    # its own deadline. Pending copper is gated and saved; the remainder is
    # reported as unfinished - the cap never loosens a rule.
    t0 = time.time()
    deadline = float(os.environ.get("LV_DEADLINE_S", "21600"))
    for attempt in range(1, 4):
        print(f"--- pass {attempt}: {len(queue)} net(s)")
        next_queue = []
        batch = []          # (netname, metrics) awaiting a DRC gate
        def gate():
            """DRC-gate the accumulated batch. Same invariant as per-net
            gating - copper that fails DRC never survives - but checked per
            4 nets: the kicad-cli run is 10-15 s and dominated finisher wall
            time. On regression the whole batch rolls back and its nets
            retry individually next pass."""
            nonlocal done_ct
            if not batch:
                return
            errs = drc_errors(PCB)
            if errs > baseline:
                # scrub-then-regate: rip exactly the violating fragments
                # (tools/scrub_fouls.py, adopt's rip at segment granularity)
                # and re-check - a batch of good nets is no longer discarded
                # for one 10-micron fragment (measured: three pour batches,
                # ~2 h of routing each, lost to a single such fragment)
                subprocess.run([sys.executable,
                                os.path.join(PROJ, "tools", "scrub_fouls.py")],
                               capture_output=True, text=True, timeout=600)
                errs = drc_errors(PCB)
            if errs > baseline:
                shutil.copyfile(LAST_GOOD, PCB)
                for n, _m in batch:
                    failed[n] = f"DRC regression in batch (+{errs - baseline})"
                    next_queue.append(n)
                print(f"  BATCH FAIL {[n for n, _ in batch]} "
                      f"(+{errs - baseline}) - rolled back")
                batch.clear()
                return
            shutil.copyfile(PCB, LAST_GOOD)
            for n, (nv, tl, man) in batch:
                failed.pop(n, None)
                done_ct += 1
                ratio = (tl / man) if man > 0.5 else 1.0
                metrics[n] = (nv, tl, man, ratio)
                flags = []
                if nv > 4:
                    flags.append("VIAS>4")
                if ratio > 2.5:
                    flags.append("RATIO>2.5")
                pct = 100 * done_ct / total_ct
                print(f"  OK {n:28} vias={nv} len={tl:5.1f} man={man:5.1f} "
                      f"ratio={ratio:4.2f} [{done_ct}/{total_ct} {pct:3.0f}%]"
                      f"{'  ' + ','.join(flags) if flags else ''}")
                if done_ct % 25 == 0:
                    git_progress(f"LV routing progress: {done_ct}/{total_ct} "
                                 f"nets ({pct:.0f}%)")
                    print(f"== progress commit at {done_ct}/{total_ct}")
            batch.clear()

        for netname in queue:
            if time.time() - t0 > deadline:
                failed.setdefault(netname, "LV deadline reached")
                next_queue.append(netname)
                continue
            args = ["--net", netname]
            ripping = rip_plan.pop(netname, None)
            if ripping:
                args += ["--rip", ";".join(ripping)]
                print(f"  RIP-RETRY {netname}: ripping {ripping}")
            try:
                r = child(args, timeout=2400 if ripping else 900)
            except subprocess.TimeoutExpired:
                gate()
                shutil.copyfile(LAST_GOOD, PCB)
                failed[netname] = "child timeout"
                next_queue.append(netname)
                print(f"  FAIL {netname:28} child timeout")
                continue
            m = re.search(r"CHILD_(OK|PARTIAL) vias=(\d+) len=([\d.]+) "
                          r"man=([\d.]+)", r.stdout)
            if not m:
                fm = re.search(r"CHILD_FAIL (.*)", r.stdout)
                cause = fm.group(1) if fm else \
                    f"child crashed (rc={r.returncode})"
                gate()
                shutil.copyfile(LAST_GOOD, PCB)
                failed[netname] = cause
                next_queue.append(netname)
                print(f"  FAIL {netname:28} {cause}")
                for l in r.stdout.splitlines():
                    if "DEBUG" in l:
                        print(f"   {l}")
                # negotiation: the pocket-walls diagnostic names whose copper
                # seals this net. Schedule ONE rip-retry for the next pass
                # with the top unlocked, unprotected wall nets.
                if not ripping:
                    # pad-seal nets first (the actual pad sealers), then the
                    # flood-boundary walls to fill up to 3 candidates
                    seal, wall = Counter(), Counter()
                    for l in r.stdout.splitlines():
                        ms = re.search(r"DEBUG pad seal \(\w+\): (\{.*\})", l)
                        mw = re.search(r"DEBUG pocket walls: (\{.*\})", l)
                        try:
                            if ms:
                                seal.update(ast.literal_eval(ms.group(1)))
                            elif mw:
                                wall.update(ast.literal_eval(mw.group(1)))
                        except (ValueError, SyntaxError):
                            pass
                    cands = []
                    for src in (seal, wall):
                        for n, _c in src.most_common():
                            if n not in ("edge/nogo", "netless") and \
                                    n not in PROTECTED and n != netname and \
                                    n not in cands:
                                cands.append(n)
                    cands = cands[:3]
                    if cands:
                        rip_plan[netname] = cands
                continue
            partial = m.group(1) == "PARTIAL"
            for rq in re.findall(r"^REQUEUE (.+)$", r.stdout, re.M):
                if rq not in next_queue:
                    next_queue.append(rq)   # pour net ripped by a rip-retry
                    failed.setdefault(rq, "ripped by a rip-retry, requeued")
            batch.append((netname,
                          (int(m.group(2)), float(m.group(3)),
                           float(m.group(4)))))
            if partial:
                next_queue.append(netname)   # resume the remainder next pass
                cm = re.search(r"cause=(.*)", r.stdout)
                print(f"  PARTIAL {netname:26} kept copper; remainder "
                      f"requeued ({cm.group(1)[:60] if cm else '?'})")
            if len(batch) >= 4:
                gate()
        gate()
        queue = next_queue
        if not queue:
            break
        if time.time() - t0 > deadline:
            print(f"LV_DEADLINE {deadline:.0f}s reached - stopping with "
                  f"{len(queue)} net(s) unfinished")
            break

    child(["--finish"], timeout=600)
    tot_v = sum(m[0] for m in metrics.values())
    flagged_v = [n for n, m in metrics.items() if m[0] > 4]
    flagged_r = [n for n, m in metrics.items() if m[3] > 2.5]
    with open(os.path.join(PROJ, "docs", "lv-route-metrics.txt"), "w") as fh:
        fh.write("LV routing metrics (tools/pcbroute_lv.py)\n")
        fh.write(f"nets routed: {done_ct}/{total_ct}   total vias: {tot_v}\n")
        fh.write(f"{'net':30} {'vias':>4} {'len mm':>8} {'manhattan':>9} "
                 f"{'ratio':>6}\n")
        for n in sorted(metrics):
            nv, tl, man, ratio = metrics[n]
            fl = (" VIAS>4" if nv > 4 else "") + \
                 (" RATIO>2.5" if ratio > 2.5 else "")
            fh.write(f"{n:30} {nv:4} {tl:8.1f} {man:9.1f} {ratio:6.2f}{fl}\n")
        if failed:
            fh.write("\nUNROUTED:\n")
            for n, c in failed.items():
                fh.write(f"  {n}: {c}\n")
    print(f"\nROUTED {done_ct}/{total_ct} nets  vias {tot_v}  "
          f"via-flags {len(flagged_v)}  ratio-flags {len(flagged_r)}")
    if failed:
        print("UNROUTED (with cause):")
        for n, c in failed.items():
            print(f"  {n}: {c}")
    print("metrics written to docs/lv-route-metrics.txt")
    print("LV_ROUTE_DONE")


if __name__ == "__main__":
    if "--net" in sys.argv:
        rip_arg = None
        if "--rip" in sys.argv:
            rip_arg = [n for n in
                       sys.argv[sys.argv.index("--rip") + 1].split(";") if n]
        main(single_net=sys.argv[sys.argv.index("--net") + 1], rip=rip_arg)
    elif "--list" in sys.argv:
        main(single_net="--list--")
    elif "--spans" in sys.argv:
        main(single_net="--spans--")
    elif "--finish" in sys.argv:
        main(single_net="--finish--")
    else:
        orchestrate()
