Immanueldavidckp/schematics/tools/deliverables.py

#!/usr/bin/env python3
"""Milestone 4 closing battery: run every gate and emit every deliverable.

Runs on the CURRENT board file (after routing completes):
  1. Full DRC (errors + warnings) -> drc-final.rpt, violations by type
  2. floorplan_check.py (the 8 approved checks)
  3. pcbroute_verify.py (locked copper identity, protected nets untouched,
     thermal via counts under U1/U5) - against autoroute-scratch if present
  4. hv_measure.py -> docs/hv-clearance-measured.txt refresh
  5. Renders: top / bottom / iso -> docs/renders/
  6. Exception list -> docs/drc-exceptions.md gets a generated section

Exit 0 only if DRC errors (unconnected included) == 0.

Run:  PYTHONPATH=tools python3 tools/deliverables.py
"""
import os
import re
import subprocess
import sys

sys.path.insert(0, os.path.dirname(os.path.abspath(__file__)))
from pcbgen import PROJ, PCB                                 # noqa: E402

RENDERS = os.path.join(PROJ, "docs", "renders")


def sh(cmd, timeout=600):
    return subprocess.run(cmd, capture_output=True, text=True,
                          timeout=timeout)


def main():
    ok = True

    # 1. full DRC
    rpt = os.path.join(PROJ, "drc-final.rpt")
    sh(["kicad-cli", "pcb", "drc", "--severity-error", "--severity-warning",
        "-o", rpt, PCB])
    text = open(rpt).read()
    kinds = {}
    for k in re.findall(r"^\[([a-z_]+)\]", text, re.M):
        kinds[k] = kinds.get(k, 0) + 1
    errs_rpt = os.path.join(PROJ, "drc-final-errors.rpt")
    sh(["kicad-cli", "pcb", "drc", "--severity-error", "-o", errs_rpt, PCB])
    etext = open(errs_rpt).read()
    ekinds = {}
    for k in re.findall(r"^\[([a-z_]+)\]", etext, re.M):
        ekinds[k] = ekinds.get(k, 0) + 1
    print(f"DRC (errors+warnings): {kinds}")
    print(f"DRC (errors only):     {ekinds}")
    if sum(ekinds.values()):
        ok = False

    # 2. floorplan checks
    r = sh([sys.executable, os.path.join(PROJ, "tools", "floorplan_check.py")],
           timeout=900)
    tail = "\n".join(r.stdout.splitlines()[-12:])
    print("--- floorplan_check tail ---")
    print(tail)
    if r.returncode != 0:
        print(f"floorplan_check rc={r.returncode}")
        ok = False

    # 3. verify (only if a scratch exists to compare)
    if os.path.exists(os.path.join(PROJ, "autoroute-scratch.kicad_pcb")):
        r = sh([sys.executable,
                os.path.join(PROJ, "tools", "pcbroute_verify.py")],
               timeout=900)
        for l in r.stdout.splitlines():
            if any(t in l for t in ("locked items", "identically",
                                    "PROTECTED", "none on", "thermal")):
                print(l)

    # 4. measured clearances
    r = sh([sys.executable, os.path.join(PROJ, "tools", "hv_measure.py")],
           timeout=900)
    with open(os.path.join(PROJ, "docs", "hv-clearance-measured.txt"),
              "w") as fh:
        fh.write("HV/MV clearances, measured from the FINAL routed board.\n"
                 "Generated by tools/hv_measure.py via tools/deliverables.py\n\n")
        fh.write(r.stdout)
    print("hv-clearance-measured.txt refreshed")

    # 5. renders
    os.makedirs(RENDERS, exist_ok=True)
    views = [("top", ["--side", "top"]),
             ("bottom", ["--side", "bottom"]),
             ("iso", ["--side", "top", "--rotate", "-45,0,45",
                      "--zoom", "0.9"])]
    for name, args in views:
        out = os.path.join(RENDERS, f"final-{name}.png")
        r = sh(["kicad-cli", "pcb", "render", "-w", "1600", "-h", "1200",
                "-o", out] + args + [PCB], timeout=900)
        print(f"render {name}: "
              f"{'ok' if os.path.exists(out) else 'FAILED ' + r.stderr[:80]}")

    print("DELIVERABLES_" + ("OK" if ok else "INCOMPLETE"))
    sys.exit(0 if ok else 3)


if __name__ == "__main__":
    main()
